quorten/megascreen/ms2vga/ms2vga.sch

## KiCad design ms2vga/ms2vga.sch (2021-03-21)

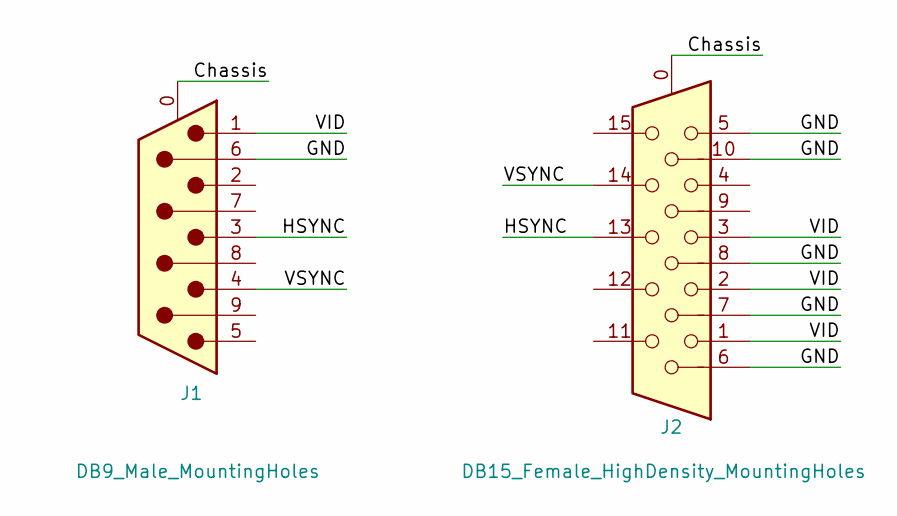
[picture p8: schematic ms2vga.sch]

Parts:
J1: DB9_Male_MountingHoles; DSUB-9_Male_Horizontal_P2.74x2.84mm_EdgePinOffset7.70mm_Hou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; MPN D09P33E4GX00LF; Digi-Key_PN 609-1481-ND
J2: DB15_Female_HighDensity_MountingHoles; DSUB-15-HD_Female_Horizontal_P2.29x1.27mm_EdgePinOffset8.35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; MPN ICD15S13E4GX00LF; Digi-Key_PN 609-5181-ND

Connections:
Chassis: J1.0 (PAD), J2.0
GND: J1.6, J2.5, J2.6, J2.7, J2.8, J2.10
HSYNC: J1.3, J2.13
VID: J1.1, J2.1, J2.2, J2.3
VSYNC: J1.4, J2.14
